GSNautilus/ammonite/media/enclosure.png

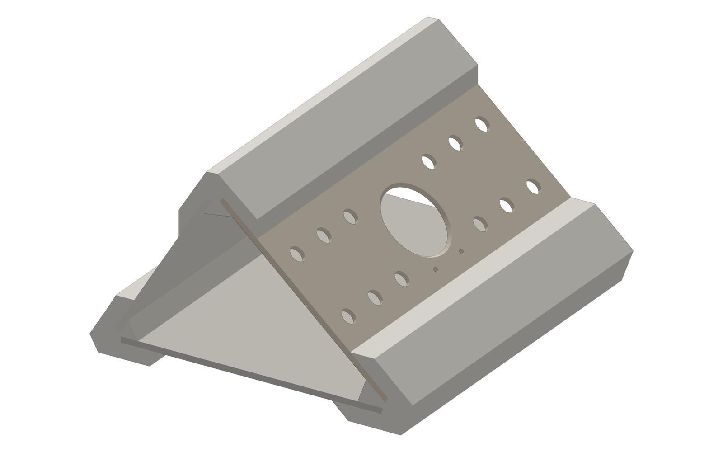
media/enclosure.png
