GSNautilus/ammonite/manual/img/panel_page_arp.png

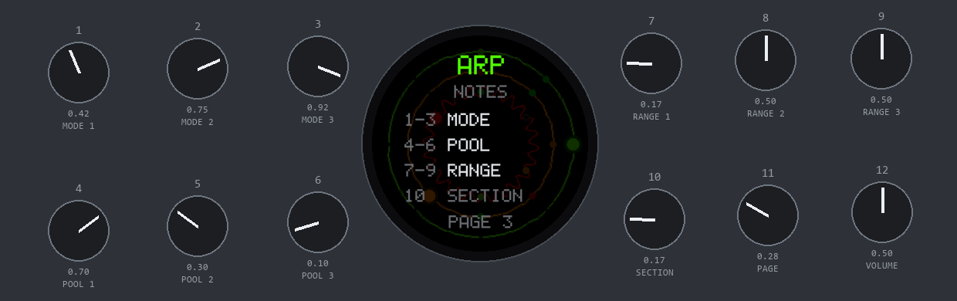
manual/img/panel_page_arp.png
