GSNautilus/ammonite/manual/img/screen_pagemap_arp.png

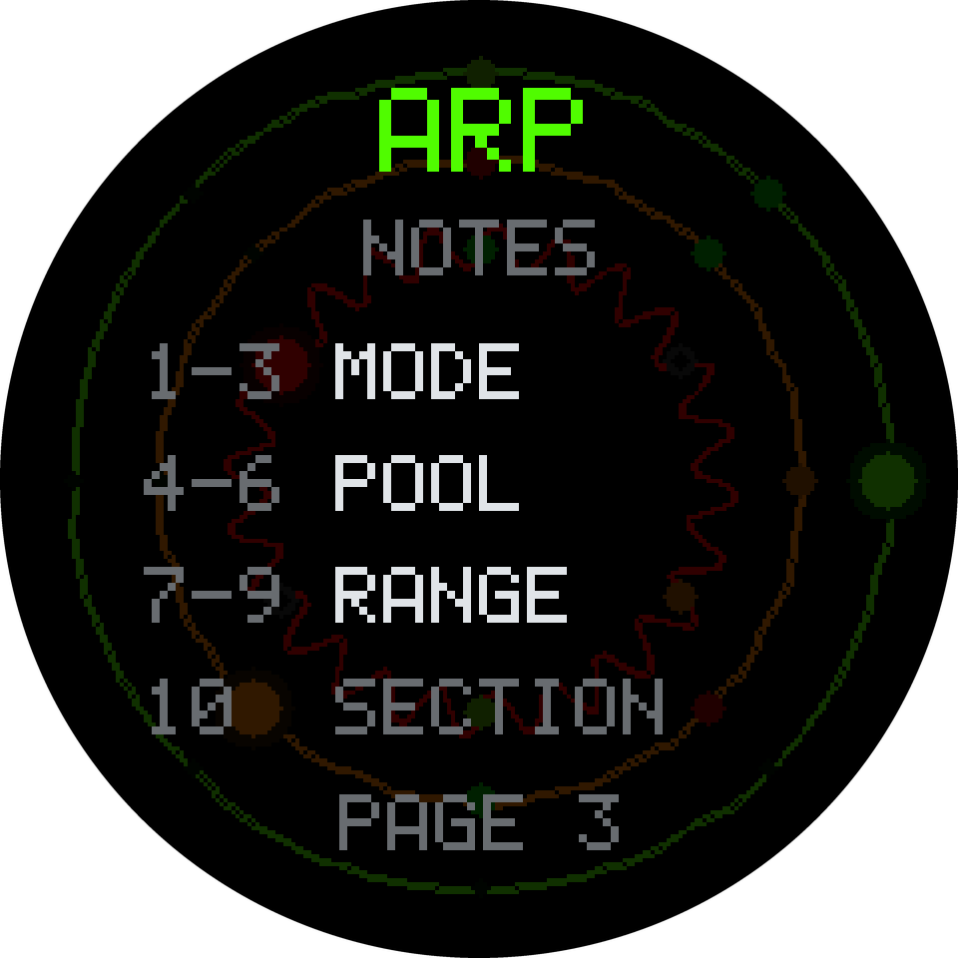
manual/img/screen_pagemap_arp.png
