GSNautilus/ammonite/manual/img/screen_pagemap_key.png

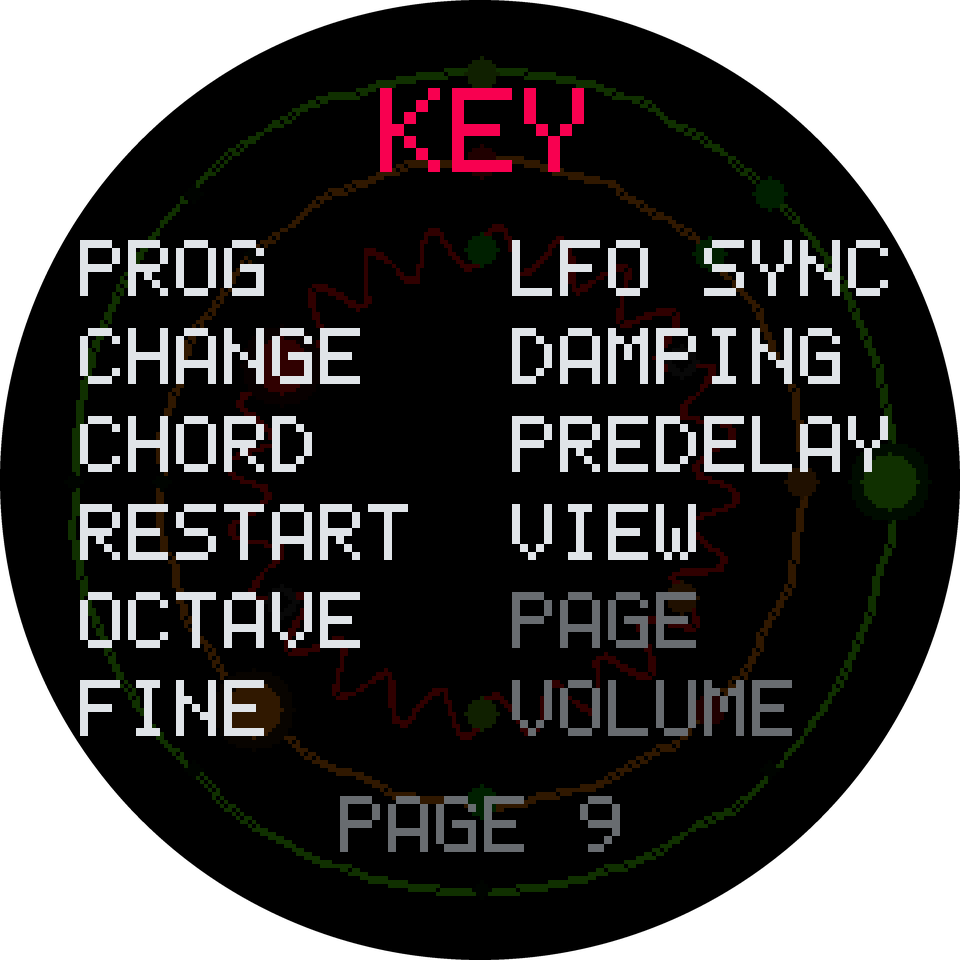
manual/img/screen_pagemap_key.png
