GSNautilus/ammonite/manual/img/screen_pagemap_main.png

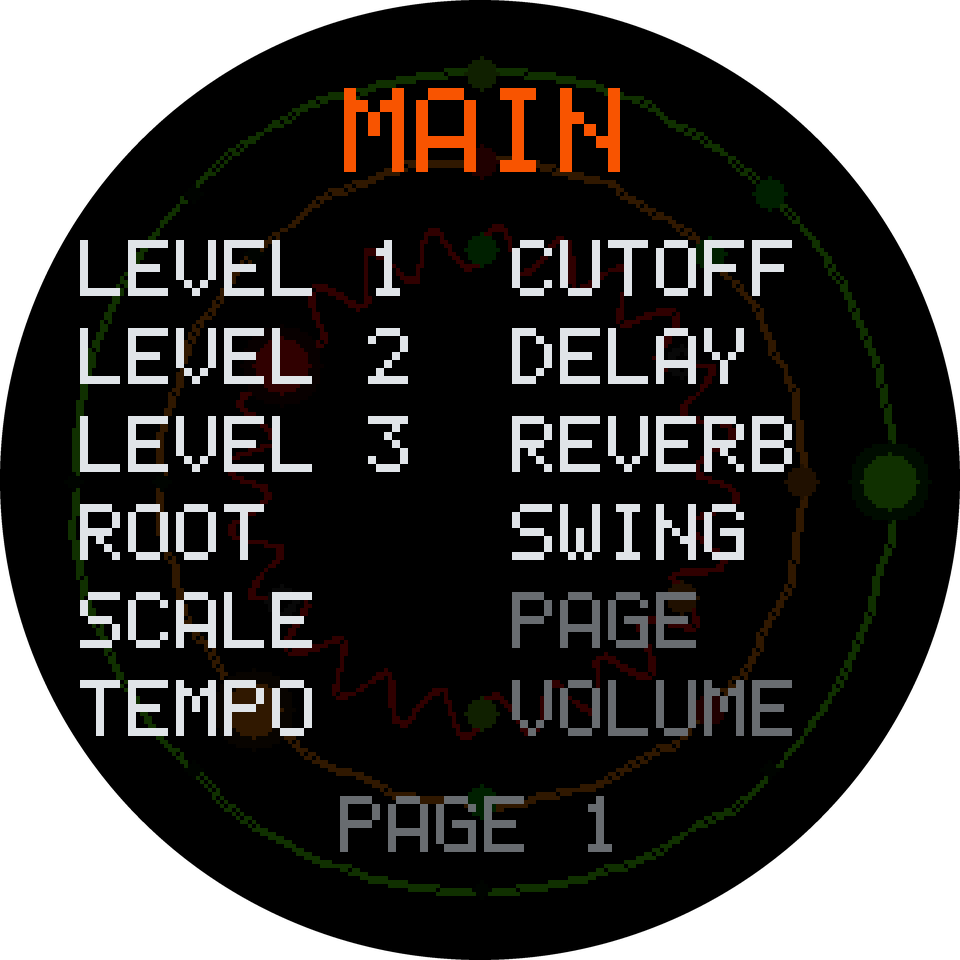
manual/img/screen_pagemap_main.png
