GSNautilus/ammonite/manual/img/screen_pagemap_mix.png

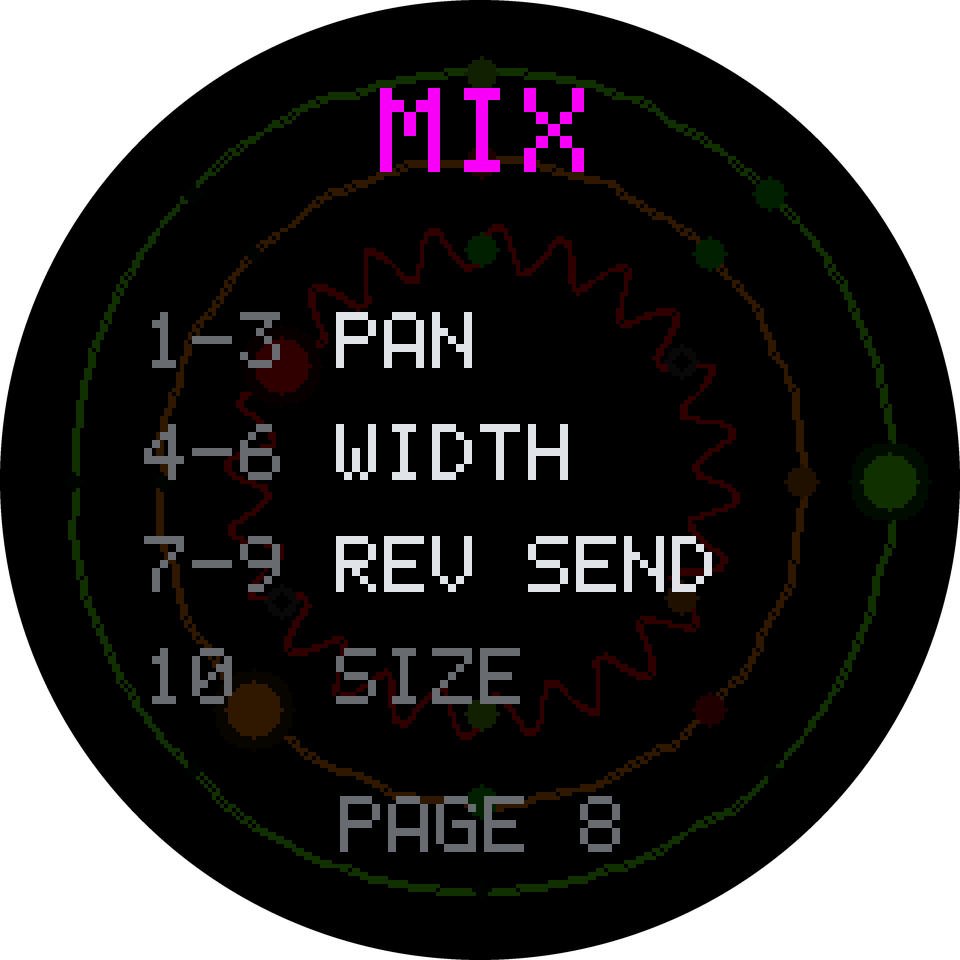
manual/img/screen_pagemap_mix.png
