GSNautilus/ammonite/manual/img/screen_recipe_bells.png

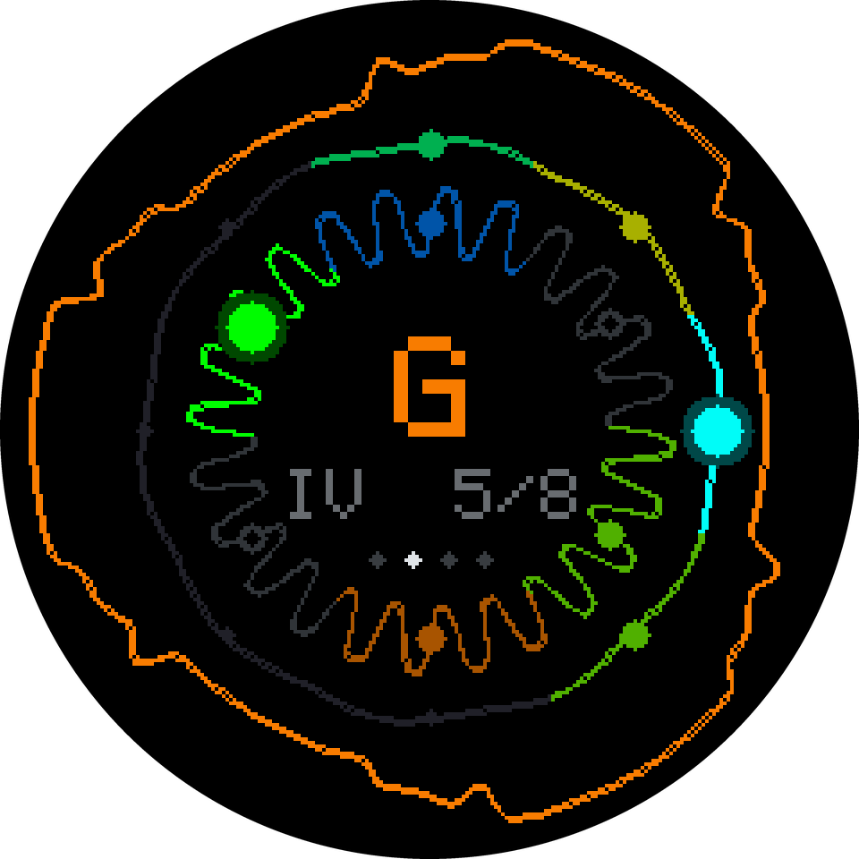
manual/img/screen_recipe_bells.png
