GSNautilus/ammonite/manual/img/screen_recipe_clockwork.png

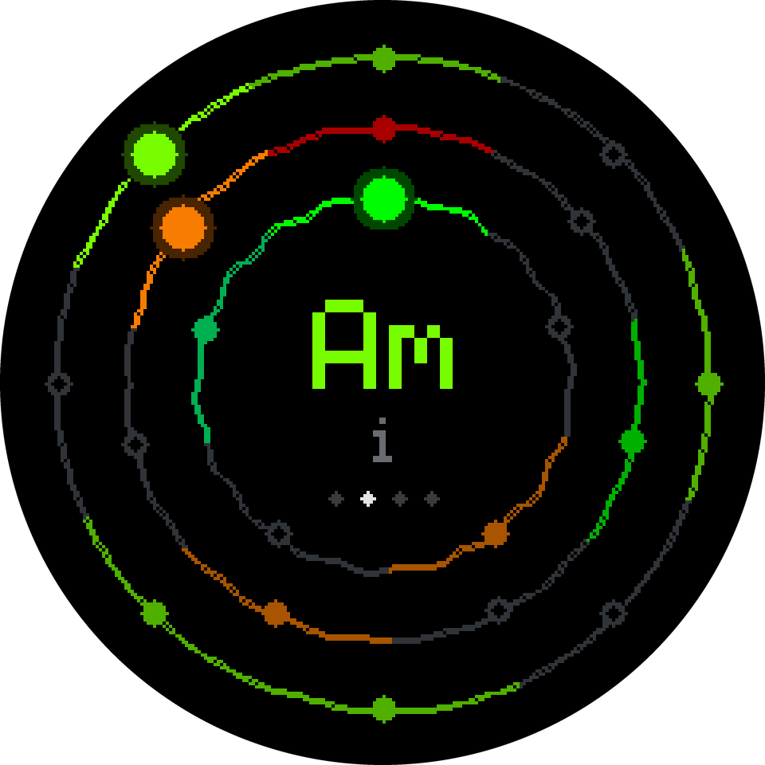
manual/img/screen_recipe_clockwork.png
