GSNautilus/ammonite/manual/img/screen_recipe_dub.png

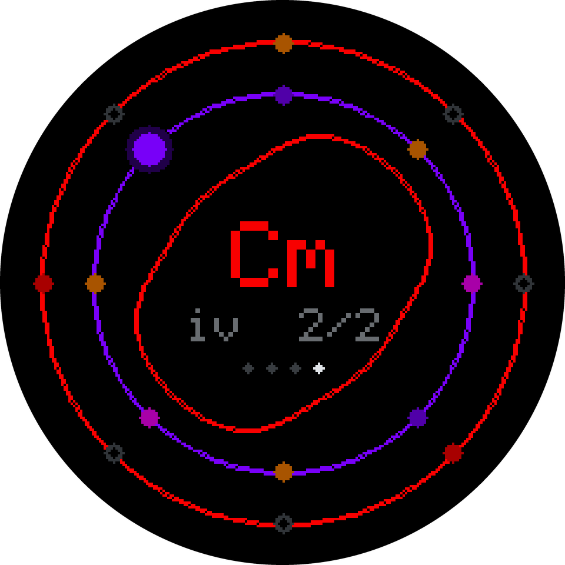
manual/img/screen_recipe_dub.png
