GSNautilus/ammonite/manual/img/screen_recipe_jazz.png

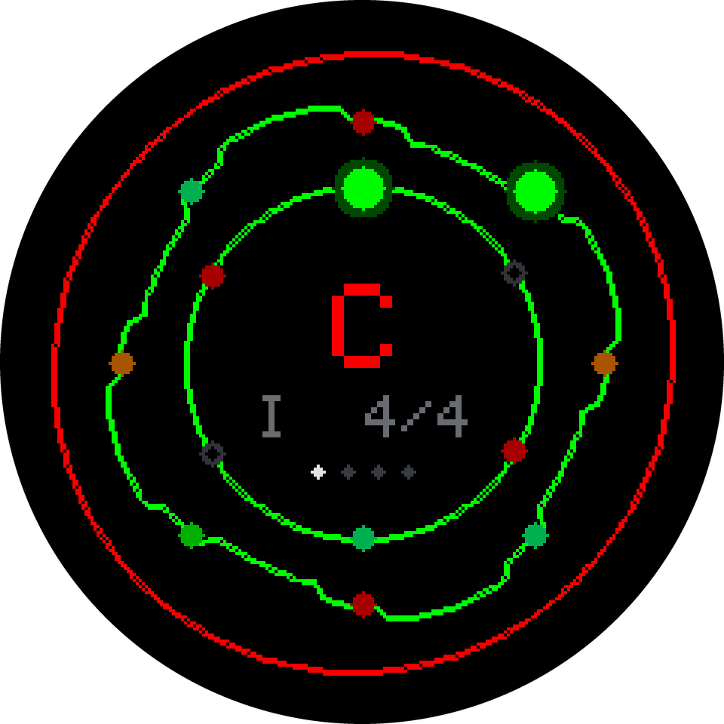
manual/img/screen_recipe_jazz.png
