GSNautilus/ammonite/manual/img/screen_recipe_tide.png

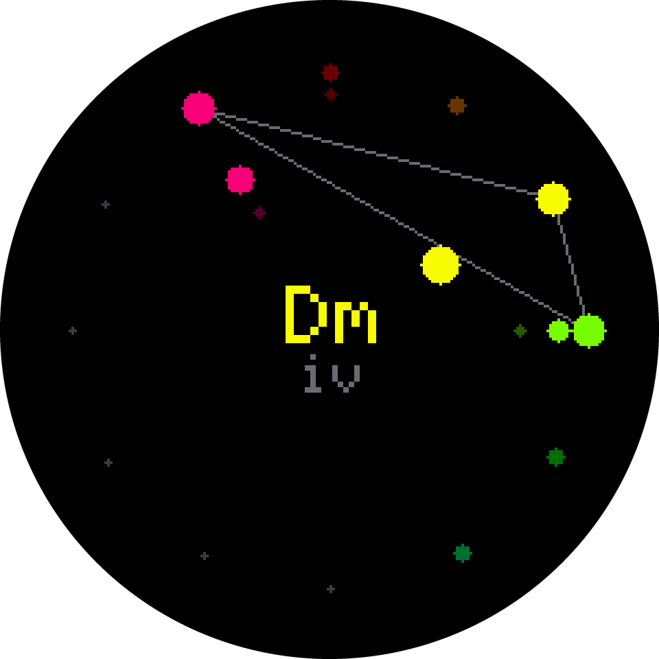
manual/img/screen_recipe_tide.png
